ru3iks/Geist/image_2026-06-06_235702359.png

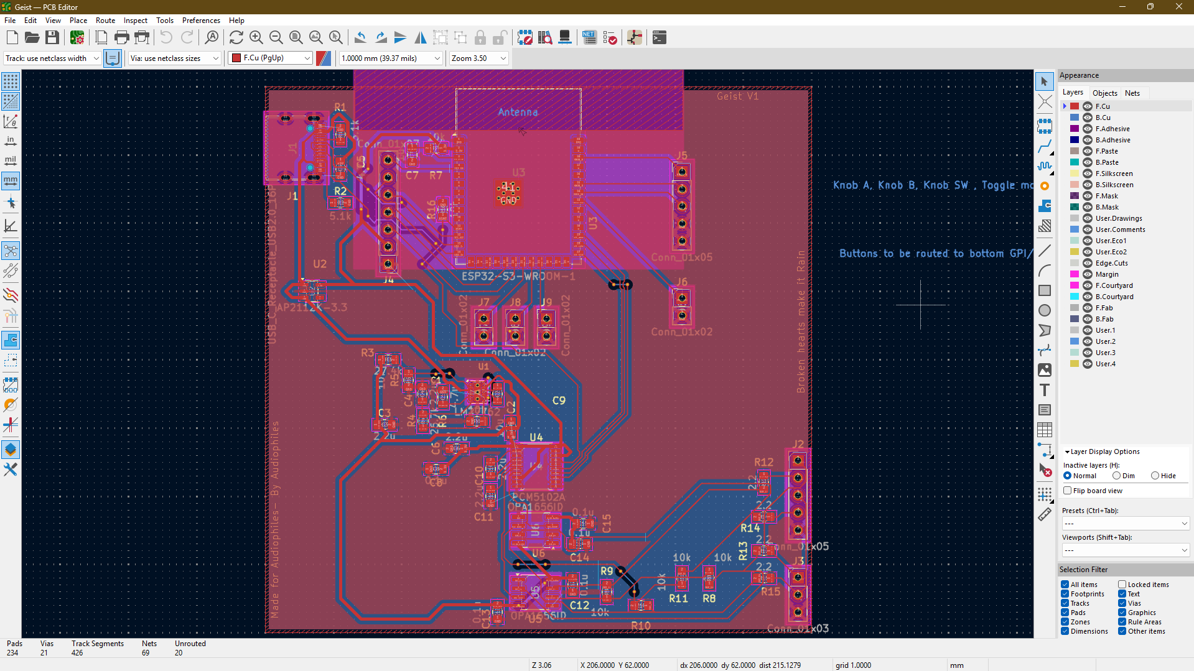
image_2026-06-06_235702359.png
